panasonic-corporation/doingio-pago/images/coral_detail_all.jpg

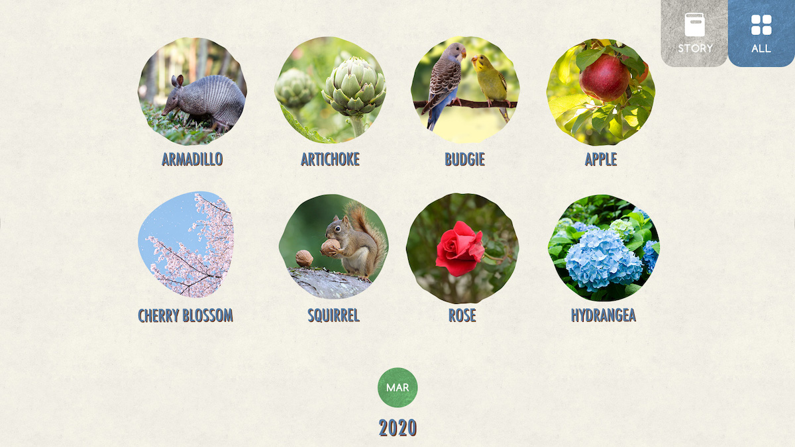
images/coral_detail_all.jpg
