panasonic-corporation/doingio-pago/images/coral_detail_day.jpg

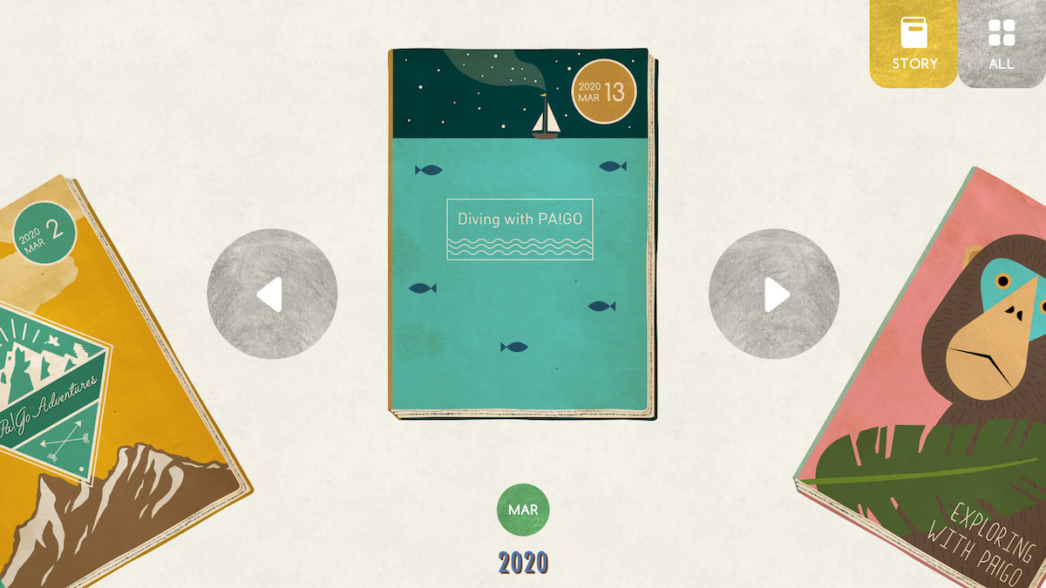
images/coral_detail_day.jpg
