panasonic-corporation/doingio-pago/images/coral_detail_detail.jpg

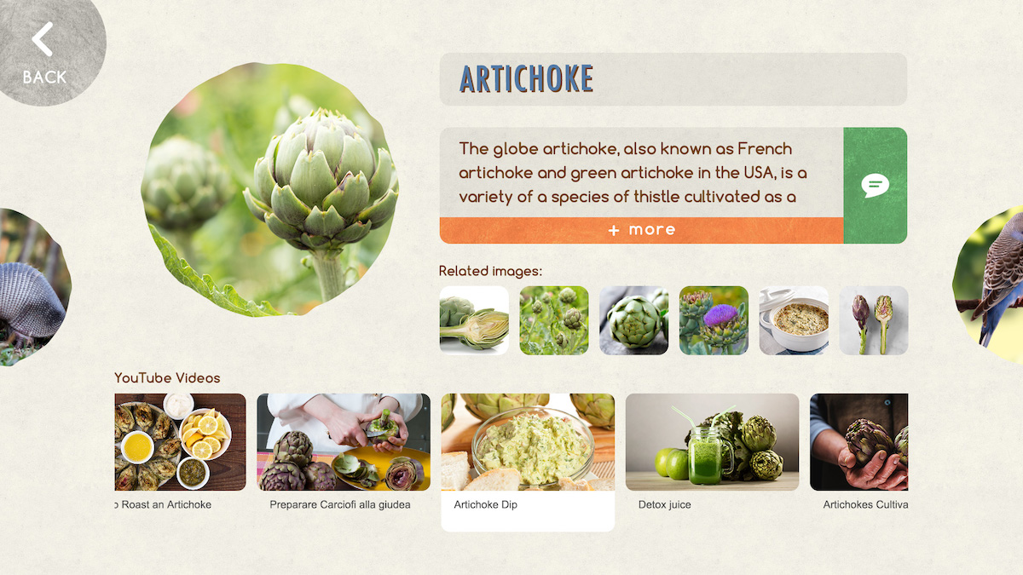
images/coral_detail_detail.jpg
